techrote/slopCAD/projects/hex-bit-stand/v3-contoured-13/README.md

# v3 — 13-pocket contoured stand

The rectangular body was removed and the outside now follows the envelope of the 4–5–4 pocket cluster.

- Capacity: **13**
- Functional pocket: **7.0 mm AF**
- Pocket depth: **12.0 mm**
- Base: **1.0 mm**
- Lead-in: **0.6 mm**, opening to **8.2 mm AF**
- Nominal outer wall margin: **3.0 mm**
- Maximum footprint: approximately **56.2 × 35.8 mm**
- Height: **13.0 mm**

## Styling

- 0.6 mm flared lower foot
- 0.6 mm recessed waist band
- 1.2 mm inset contoured top chamfer

All features are support-free and selected with a 0.6 mm nozzle in mind.
