techrote/slopCAD/projects/hex-bit-stand/v4-dense-51/hex_bit_stand_dense_51_v4.stl

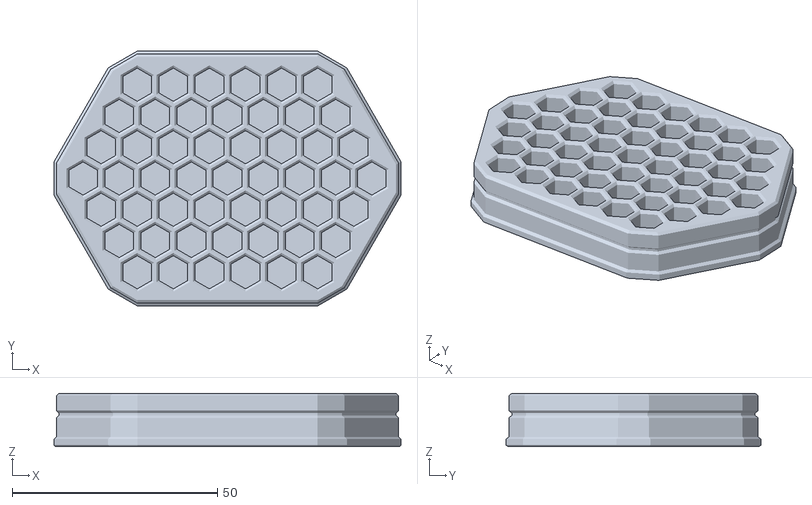
[picture p17: CAD file, 2026-10-03]
projects/hex-bit-stand/v4-dense-51/hex_bit_stand_dense_51_v4.stl
84.6 x 62.1 x 13.0
