techrote/slopCAD/projects/hex-bit-stand/v5-dense-contoured-13/hex_bit_stand_dense_contoured_13_v6.stl

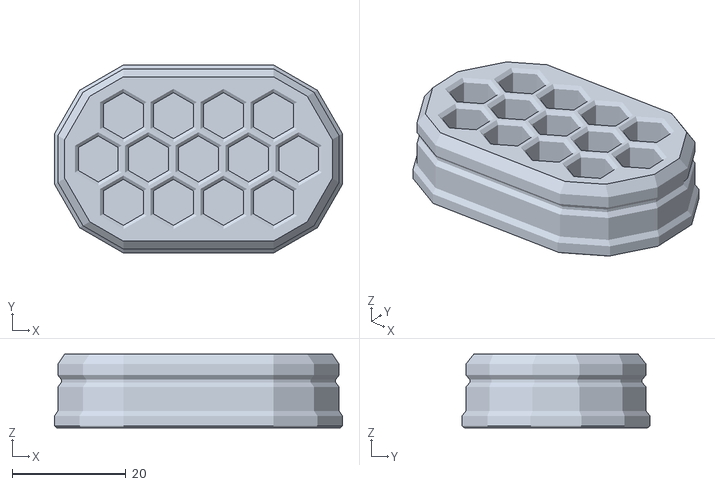
[picture p18: CAD file, 2026-10-03]
projects/hex-bit-stand/v5-dense-contoured-13/hex_bit_stand_dense_contoured_13_v6.stl
50.6 x 33.0 x 13.0
