techrote/slopCAD/projects/hex-bit-stand/v6-outward-tilted-13/hex_bit_stand_outward_tilted_13_v6.stl

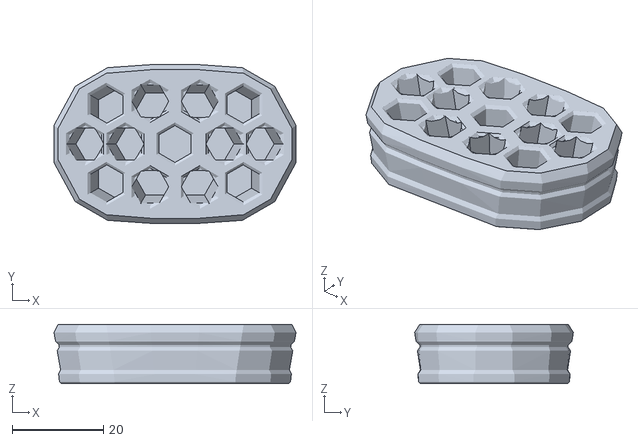
[picture p19: CAD file, 2026-10-07]
projects/hex-bit-stand/v6-outward-tilted-13/hex_bit_stand_outward_tilted_13_v6.stl
53.0 x 34.8 x 13.0
