techrote/slopCAD/projects/hex-bit-stand/v7-material-efficient-51/hex_bit_stand_material_efficient_51_v7.stl

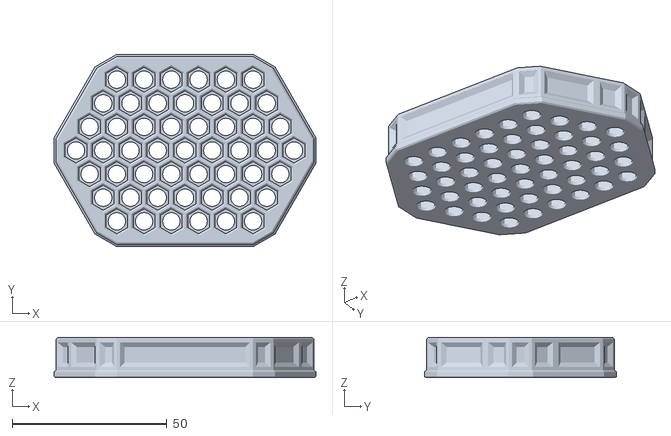
[picture p20: CAD file, 2026-10-07]
projects/hex-bit-stand/v7-material-efficient-51/hex_bit_stand_material_efficient_51_v7.stl
84.6 x 62.1 x 13.0
