techrote/slopCAD/projects/hex-bit-stand/v8-tiered-tilt-19/hex_bit_stand_tiered_tilt_19_v8.stl

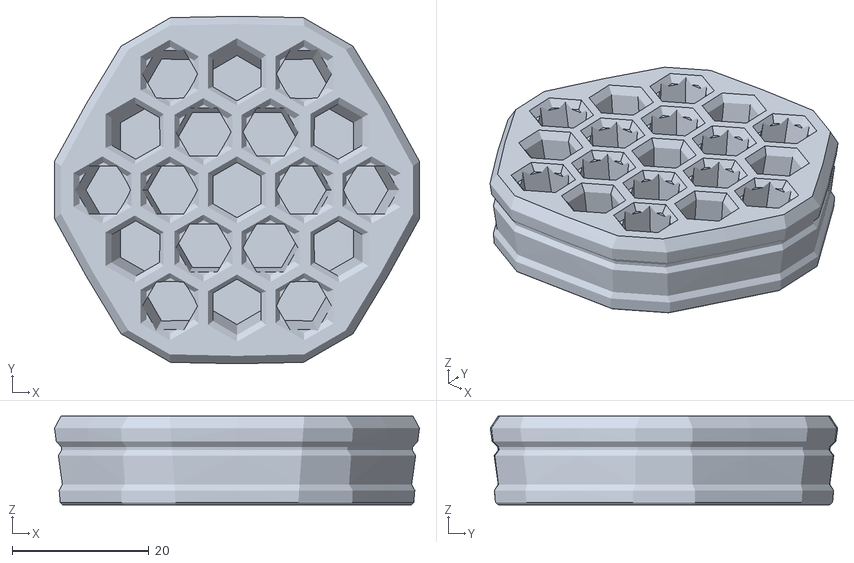
[picture p21: CAD file, 2026-10-07]
projects/hex-bit-stand/v8-tiered-tilt-19/hex_bit_stand_tiered_tilt_19_v8.stl
53.4 x 50.8 x 13.0
