techrote/slopCAD/projects/hex-bit-stand/v9-effect-plate-19/hex_bit_stand_effect_plate_19_v9.stl

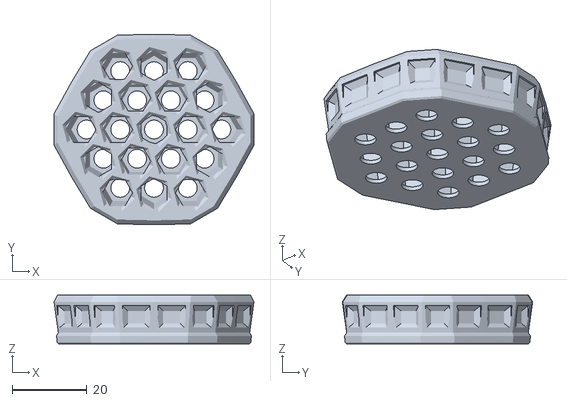
[picture p22: CAD file, 2026-10-07]
projects/hex-bit-stand/v9-effect-plate-19/hex_bit_stand_effect_plate_19_v9.stl
53.4 x 50.8 x 13.0
